NanoleafTechnologies/SatX-Technologies/OpenDatasets/Borrehaugene/Humidity (altitude).PNG

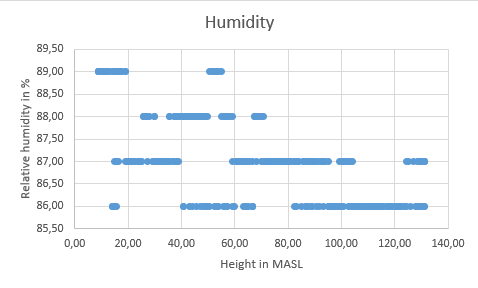
OpenDatasets/Borrehaugene/Humidity (altitude).PNG
