NanoleafTechnologies/SatX-Technologies/OpenDatasets/Borrehaugene/Temperature (altitude).PNG

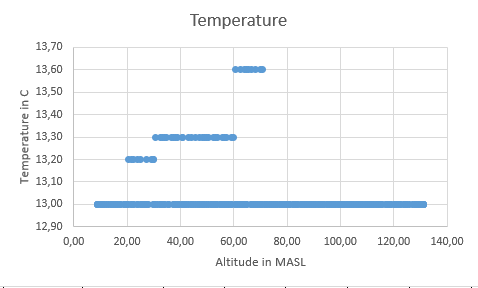
OpenDatasets/Borrehaugene/Temperature (altitude).PNG
