NanoleafTechnologies/SatX-Technologies/OpenDatasets/Borrehaugene/UV-radiation (altitude) (1).PNG

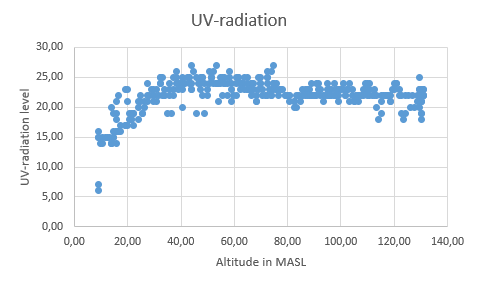
OpenDatasets/Borrehaugene/UV-radiation (altitude) (1).PNG
