NanoleafTechnologies/SatX-Technologies/OpenDatasets/Slottsfjell/Humidity (altitude) (1).PNG

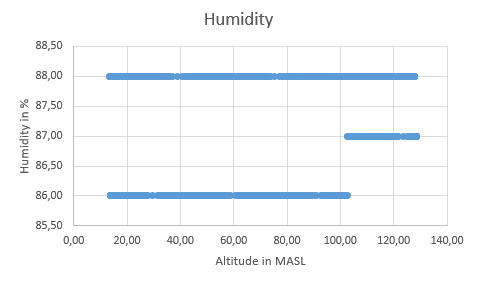
OpenDatasets/Slottsfjell/Humidity (altitude) (1).PNG
