NanoleafTechnologies/SatX-Technologies/OpenDatasets/Slottsfjell/Pressure (cBar).PNG

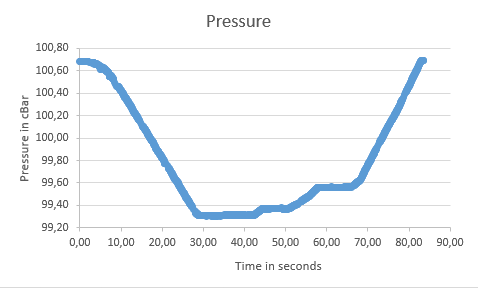
OpenDatasets/Slottsfjell/Pressure (cBar).PNG
