NanoleafTechnologies/SatX-Technologies/OpenDatasets/Slottsfjell/Temperature (time).PNG

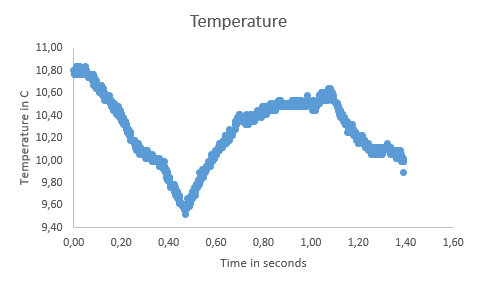
OpenDatasets/Slottsfjell/Temperature (time).PNG
