NanoleafTechnologies/SatX-Technologies/SatelliteCode/Camera/ESP32-CAM_1024x1024.jpg

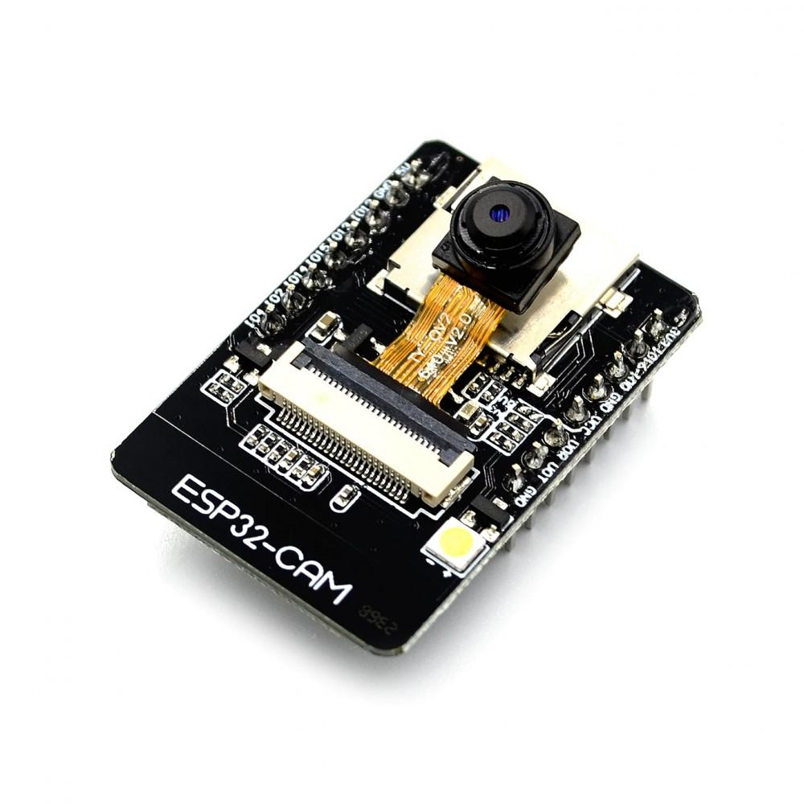
SatelliteCode/Camera/ESP32-CAM_1024x1024.jpg
